davidzindovic/Educational-staircase/Examples/stopmotion/prva_animacija/1.jpg

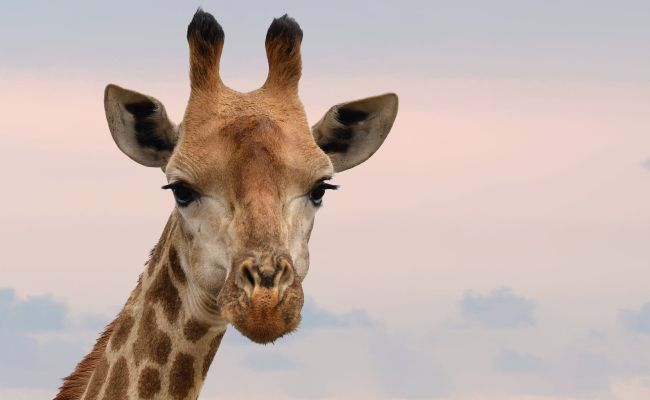
Examples/stopmotion/prva_animacija/1.jpg
