davidzindovic/Educational-staircase/Examples/stopmotion/prva_animacija/2.jpg

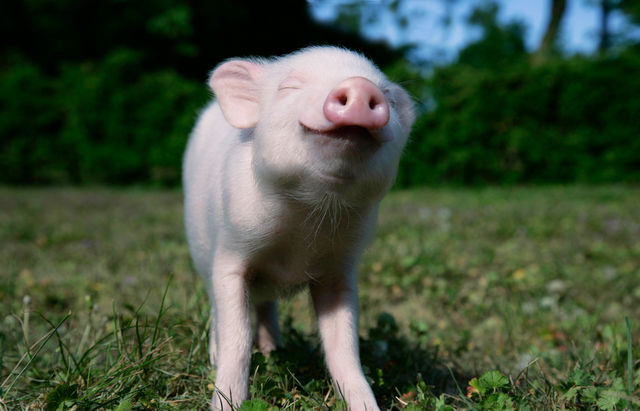
Examples/stopmotion/prva_animacija/2.jpg
