davidzindovic/Educational-staircase/Examples/stopmotion/prva_animacija/4.jpg

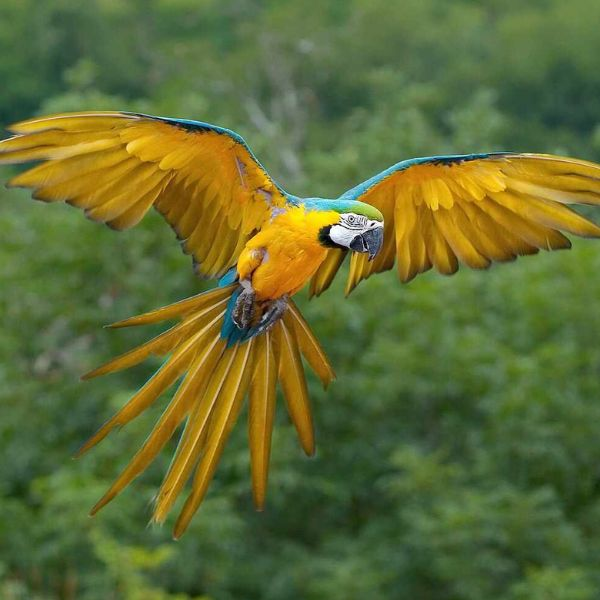
Examples/stopmotion/prva_animacija/4.jpg
