davidzindovic/Educational-staircase/Examples/stopmotion/prva_animacija/5.jpg

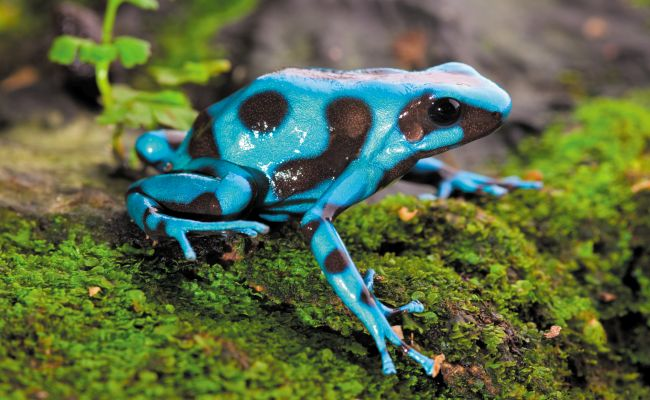
Examples/stopmotion/prva_animacija/5.jpg
